abboju-nikhil/3v3-500mA-LDO/Checks/DRC Checks.png

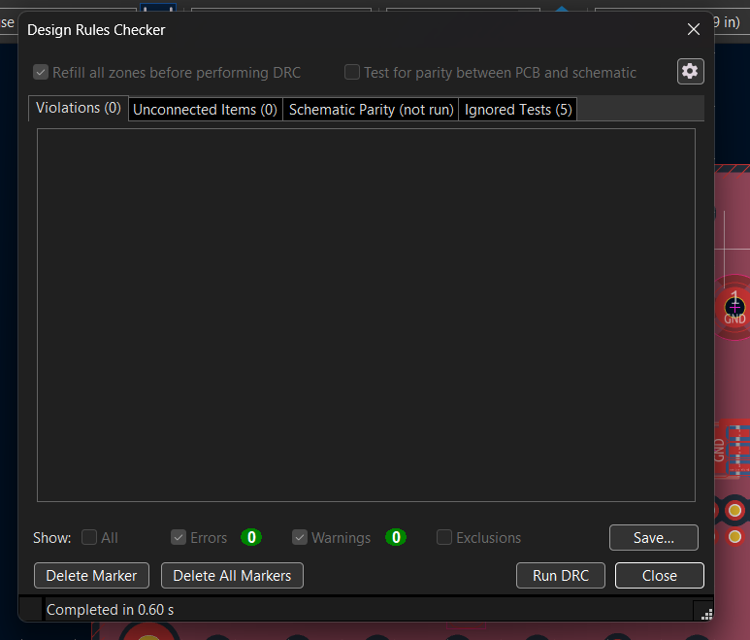
Checks/DRC Checks.png
