abboju-nikhil/3v3-500mA-LDO/Checks/ERC checks.png

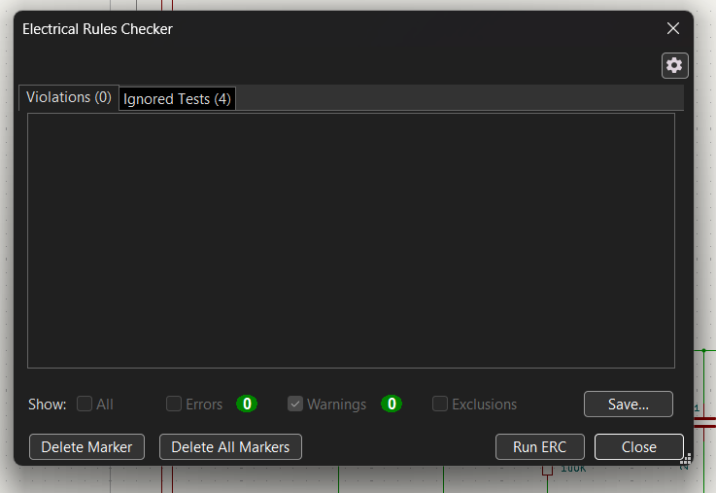
Checks/ERC checks.png
