abboju-nikhil/3v3-500mA-LDO/Layout/3D image back.png

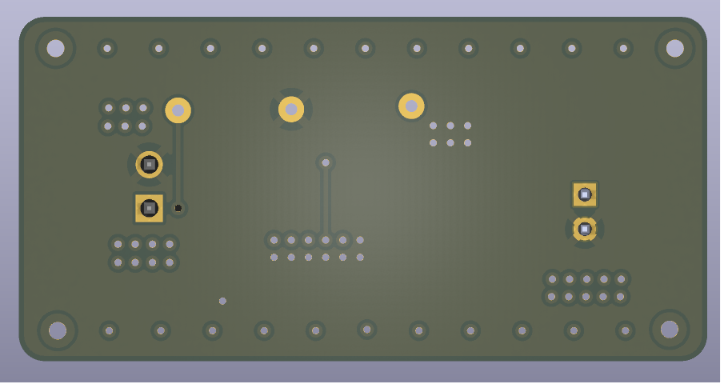
Layout/3D image back.png
