abboju-nikhil/3v3-500mA-LDO/Layout/Bcu.png

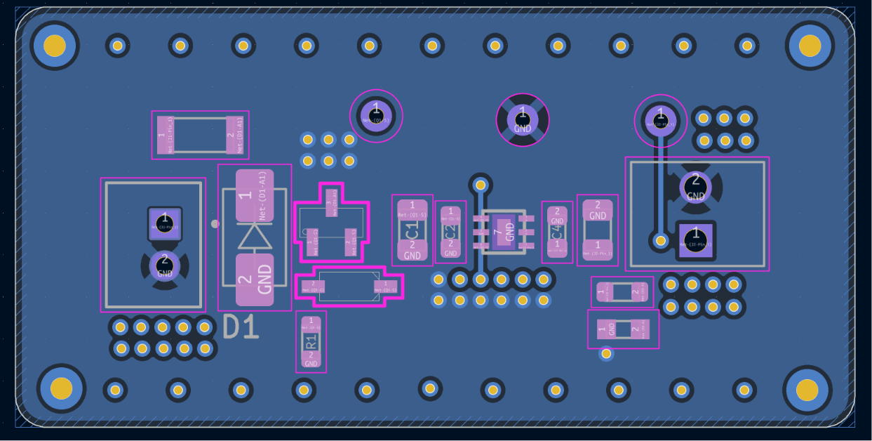
Layout/Bcu.png
